rareval48/JukeboxRepo/images/assembly_images/front_side_off.jpg

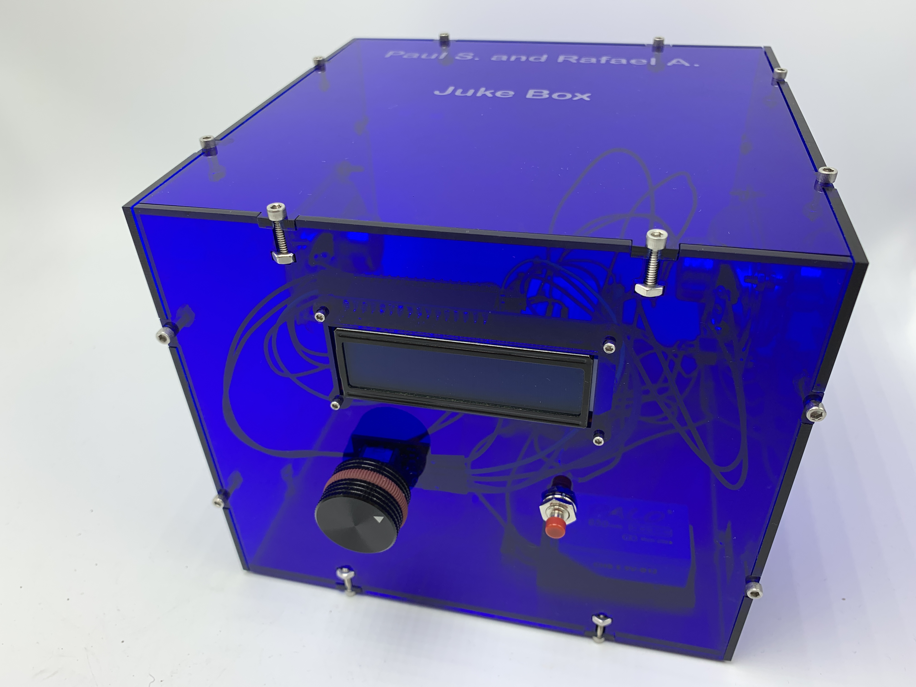
images/assembly_images/front_side_off.jpg
